MichaelRol/PuzzleLink-by-Team-TINY/Images/heuristic2.jpg

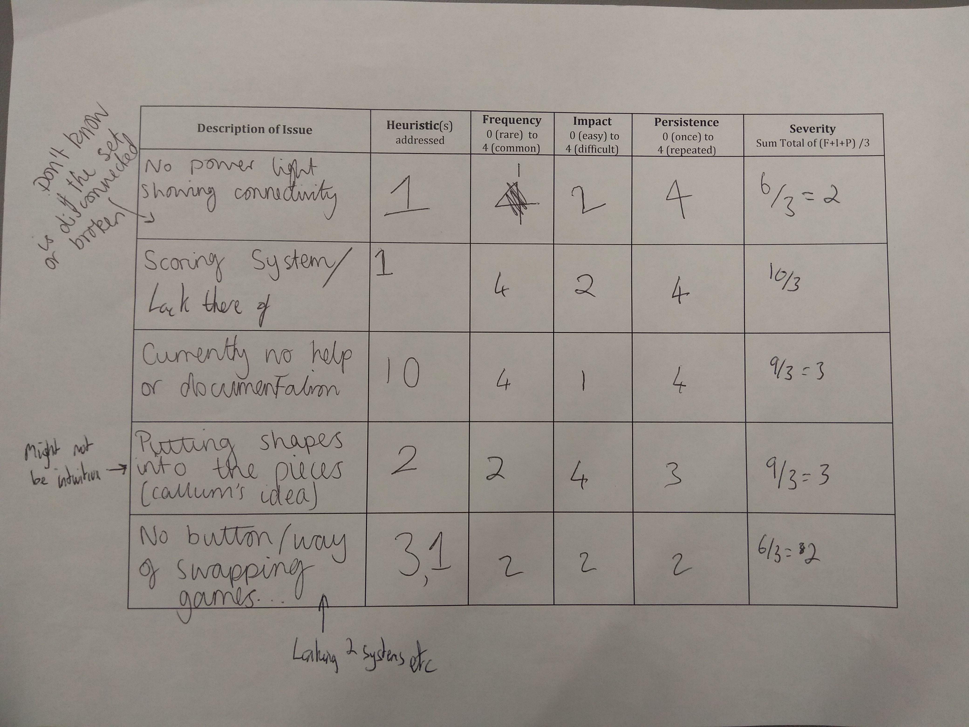
Images/heuristic2.jpg
