MichaelRol/PuzzleLink-by-Team-TINY/Images/heuristic3.jpg

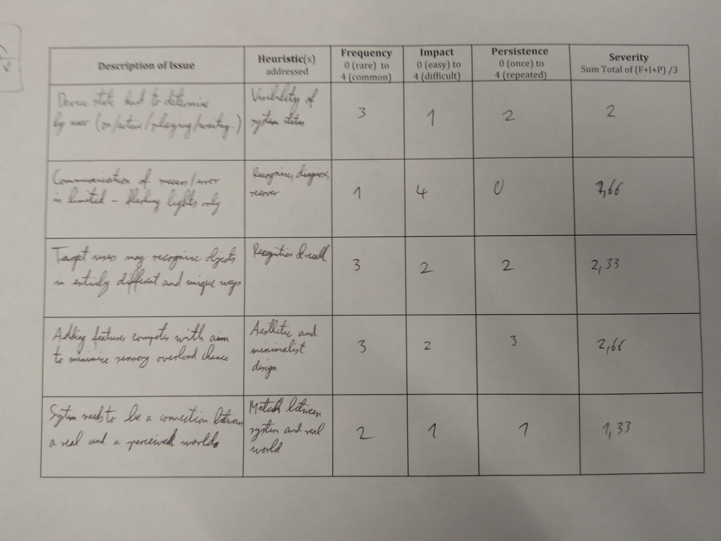
Images/heuristic3.jpg
