MichaelRol/PuzzleLink-by-Team-TINY/Images/PrototypingDrawing.jpg

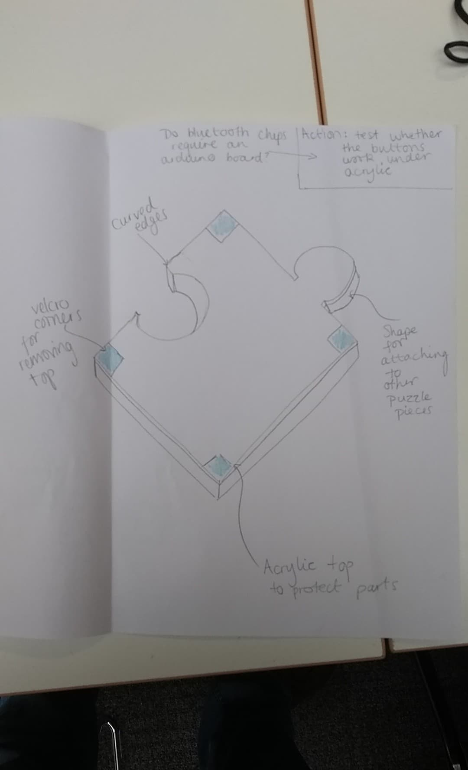
Images/PrototypingDrawing.jpg
